kingsabra/Hydraulic-Pump-Design/cad/piston screw.SLDPRT

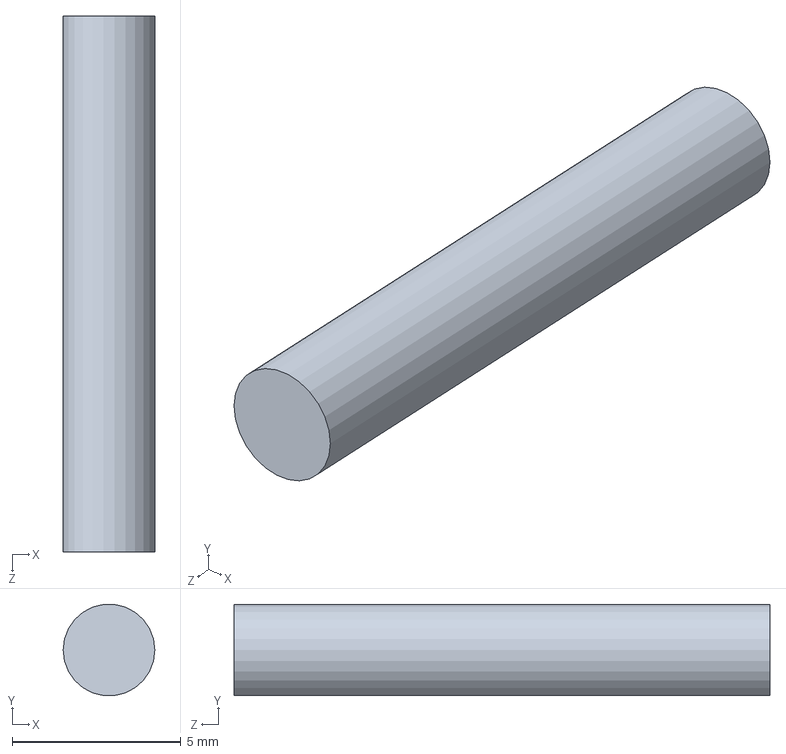
[picture p15: CAD file, 2026-03-06]
cad/piston screw.SLDPRT
2.72 x 2.70 x 15.9 mm
