kingsabra/Hydraulic-Pump-Design/cad/screws/5454K650_MINIATURE BRASS FITTING.SLDPRT

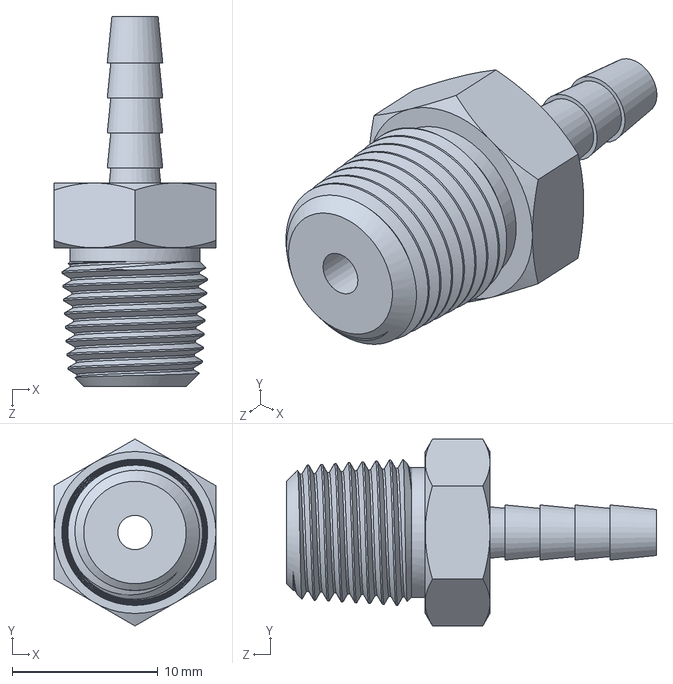
[picture p16: CAD file, 2026-03-06]
cad/screws/5454K650_MINIATURE BRASS FITTING.SLDPRT
11.1 x 12.8 x 25.4 mm
